Elecrow-RD/CrowPanel-ESP32-1.54-E-paper-HMI-Display-with-152-152/factory_soucecode/1.54_tow/pic/154/154/NEW_UI_1-54_BW_拨轮页面-01.bmp

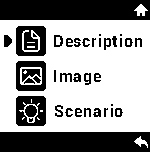
factory_soucecode/1.54_tow/pic/154/154/NEW_UI_1-54_BW_拨轮页面-01.bmp
