Elecrow-RD/CrowPanel-ESP32-1.54-E-paper-HMI-Display-with-152-152/factory_soucecode/1.54_tow/pic/NEW_UI_1-54_BW_/NEW_UI_1-54_BW_img-04.bmp

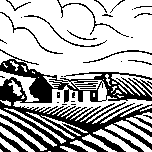
factory_soucecode/1.54_tow/pic/NEW_UI_1-54_BW_/NEW_UI_1-54_BW_img-04.bmp
