Elecrow-RD/CrowPanel-ESP32-1.54-E-paper-HMI-Display-with-152-152/factory_soucecode/1.54_tow/pic/ui_1-54_BW/UI_1-54_BW_img-06.bmp

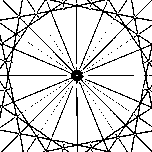
factory_soucecode/1.54_tow/pic/ui_1-54_BW/UI_1-54_BW_img-06.bmp
