Elecrow-RD/CrowPanel-ESP32-1.54-E-paper-HMI-Display-with-152-152/factory_soucecode/1.54_tow/main/pic_image.h

const unsigned char gImage_image[2888] = { /* 0X00,0X01,0X98,0X00,0X98,0X00, */
0X00,0X00,0X00,0X1C,0X00,0X00,0X01,0XC0,0X00,0X00,0X00,0X06,0X00,0X00,0X00,0X00,
0X00,0X00,0XC0,0X00,0X00,0X00,0X07,0X00,0X00,0X07,0X00,0X00,0X00,0X00,0X04,0X00,
0X00,0X00,0X00,0X00,0X03,0X80,0X00,0X00,0X00,0X01,0X80,0X00,0X0C,0X00,0X00,0X00,
0X00,0X0C,0X00,0X00,0X00,0X70,0X00,0X06,0X00,0X00,0X00,0X00,0X00,0XC0,0X00,0X18,
0X00,0X01,0XFF,0XE0,0X08,0X00,0X00,0X00,0X0E,0X00,0X0C,0X00,0X00,0X00,0X00,0X00,
0X60,0X00,0X30,0X00,0X0F,0X80,0X7C,0X18,0X00,0X00,0X00,0X03,0X80,0X08,0X00,0X00,
0X00,0X00,0X00,0X10,0X00,0X60,0X00,0X3C,0X00,0X07,0X10,0X00,0X00,0X00,0X00,0XE0,
0X18,0X00,0XFF,0XF0,0X00,0X00,0X08,0X00,0XC0,0X00,0X70,0X00,0X01,0XB0,0X00,0X00,
0X00,0X00,0X38,0X30,0X00,0X00,0X1F,0X00,0X00,0X04,0X00,0X80,0X00,0XC0,0X00,0X00,
0XE0,0X00,0X00,0X00,0X00,0X0E,0X20,0X00,0X00,0X00,0XC0,0X00,0X02,0X01,0X00,0X01,
0X80,0X00,0X00,0X20,0X00,0X00,0X00,0X00,0X03,0X60,0X00,0X00,0X00,0X10,0X00,0X01,
0X03,0X00,0X03,0X00,0X00,0X00,0X20,0X00,0X00,0X00,0X00,0X01,0XC0,0X00,0X00,0X00,
0X00,0X00,0X01,0X02,0X00,0X06,0X00,0X00,0X00,0X60,0X00,0X00,0X00,0X00,0X00,0XC0,
0X00,0X00,0X00,0X00,0X00,0X00,0X86,0X00,0X0C,0X00,0X00,0X00,0X60,0X00,0X00,0X00,
0X00,0X00,0X00,0X00,0X00,0X00,0X00,0X00,0X00,0X44,0X00,0X18,0X00,0X00,0X00,0X60,
0X00,0X00,0X00,0X00,0X00,0X00,0X07,0X3F,0XE0,0X00,0X00,0X00,0X00,0X00,0X10,0X00,
0X00,0X00,0X40,0X00,0X00,0X00,0X00,0X00,0X00,0X1C,0XF0,0X7C,0X00,0X00,0X00,0X0F,
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
0X00,0X00,0X00,0X03,0XFF,0XFF,0XF0,0X00,0X01,0XE0,0X00,0X0C,0X00,0X00,0X00,0X00,
0X00,0XE0,0X00,0X00,0X00,0X00,0X00,0X7F,0XFE,0X00,0X00,0X00,0XF0,0X00,0X06,0X00,
0X00,0X00,0X00,0X00,0X78,0X00,0X00,0X00,0X00,0X00,0X07,0X80,0X00,0X00,0X00,0X78,
0X00,0X01,0X00,0X00,0X00,0X00,0X00,0X1E,};
