Elecrow-RD/CrowPanel-ESP32-1.54-E-paper-HMI-Display-with-152-152/factory_soucecode/1.54_tow/main/pic_scenario.h

const unsigned char gImage_scenario_home[2888] = { /* 0X00,0X01,0X98,0X00,0X98,0X00, */
0XFF,0XFF,0XFF,0XFF,0XFF,0XFF,0XFF,0XFF,0XFF,0XFF,0XFF,0XFF,0XFF,0XFF,0XFF,0XFF,
0XFF,0XFF,0XFF,0XFF,0XFF,0XFF,0XFF,0XFF,0XFF,0XFF,0XFF,0XFF,0XFF,0XFF,0XFF,0XFF,
0XFF,0XFF,0XFF,0XFF,0XFF,0XFF,0XFF,0XFF,0XFF,0XFF,0XFF,0XFF,0XFF,0XFF,0XFF,0XFF,
0XFF,0XFF,0XFF,0XFF,0XFF,0XFF,0XFF,0XE7,0XFF,0XFF,0XFF,0XFF,0XFF,0XFF,0XFF,0XFF,
0XFF,0XFF,0XFF,0XFF,0XFF,0XFF,0XFF,0XFF,0XFF,0XFF,0XE7,0XFF,0XFF,0XCF,0XFF,0XFF,
0XF3,0XFF,0XFF,0XFF,0XFF,0XFF,0XFF,0XFF,0XFF,0XFF,0XFF,0XFF,0XFC,0XFF,0X3F,0XFF,
0X87,0XFF,0XFF,0XF3,0XFF,0XFF,0X9F,0XFF,0XFF,0X0F,0XFF,0XFF,0XFF,0XFF,0XF9,0XFE,
0X81,0X7F,0XFF,0X03,0XFF,0XFF,0XF3,0XFF,0XFF,0X9F,0XFF,0XFE,0X47,0XFF,0XFF,0XFF,
0XFF,0XF9,0XFF,0X3C,0XFF,0XFE,0X01,0XFF,0XFF,0XF3,0XC3,0XD7,0X0E,0X2E,0X1C,0XE7,
0XF8,0XB8,0X8B,0XE3,0XF9,0XFF,0X7E,0XFF,0XFC,0X00,0XFF,0XFF,0XF3,0XC9,0XE7,0X9C,
0X4E,0X4F,0XF7,0XF1,0X39,0X13,0XC9,0XF9,0XFE,0X7E,0X7F,0XF8,0X00,0X7F,0XFF,0XF3,
0X9D,0XE7,0X9C,0XCC,0XEF,0XF7,0XF3,0X33,0X33,0XCF,0XF9,0XF2,0X7E,0X4F,0XF0,0X00,
0X3F,0XFF,0XF3,0X9C,0XE7,0X9C,0XCC,0XE7,0XF7,0XF3,0X33,0X33,0XC1,0XF9,0XFE,0X7E,
0X7F,0XFE,0X01,0XFF,0XFF,0XF3,0X9D,0XE7,0X9C,0XCC,0XEC,0XE7,0XF3,0X33,0X33,0XCC,
0XF9,0XFF,0X3E,0XFF,0XFE,0X01,0XFF,0XFF,0XF3,0XC9,0XE7,0X9C,0XCE,0X4E,0X47,0XF1,
0X33,0X33,0XC8,0XF9,0XFF,0XBD,0XFF,0XFE,0X31,0XFF,0XFF,0XF3,0XC3,0XE7,0X3C,0XCE,
0X1F,0X0F,0XF8,0X33,0X33,0XD1,0X81,0XFE,0X9F,0X7F,0XFE,0X31,0XFF,0XFF,0XFF,0XFF,
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
0X00,0X80,0X20,0X99,0X87,0XF9,0X00,0X00,0X80,0X20,0X99,0X07,0XF9,0X00,0X00,0XC0,
0X20,0X8E,0X03,0XF3,0X00,0X00,0X40,0X00,0X00,0X01,0XE2,0X00,0X00,0X20,0X00,0X00,
0X00,0X04,0X00,0X00,0X18,0X00,0X00,0X00,0X18,0X00,0X00,0X0F,0XFF,0XFF,0XFF,0XF0,
0X00,0X00,};
