Elecrow-RD/CrowPanel-ESP32-1.54-E-paper-HMI-Display-with-152-152/example/arduino/Example/1.54_Global_refresh/Pic.h

const unsigned char gImage_1[2888] = { /* 0X00,0X01,0X98,0X00,0X98,0X00, */
0XFF,0XFF,0XFF,0XFF,0XFF,0XFF,0XFF,0XFF,0XFF,0XFF,0XFF,0XFF,0XFF,0XFF,0XFF,0XFF,
0XFF,0XFF,0XFF,0XFF,0XFF,0XFF,0XFF,0XFF,0XFF,0XFF,0XFF,0XFF,0XFF,0XFF,0XFF,0XFF,
0XFF,0XFF,0XFF,0XFF,0XFF,0XFF,0XFF,0XFF,0XFF,0XFF,0XFF,0XFF,0XFF,0XFF,0XFF,0XFF,
0XFF,0XFF,0XFF,0XFF,0XFF,0XFF,0XFF,0XFF,0XFF,0XFF,0XFF,0XFF,0XFF,0XFF,0XFF,0XFF,
0XFF,0XFF,0XFF,0XFF,0XFF,0XFF,0XFF,0XFF,0XFF,0XFF,0XFF,0XFF,0XFF,0XFF,0XFF,0XFF,
0XFF,0XFF,0XFF,0XFF,0XFF,0XFF,0XFF,0XFF,0XFF,0XFF,0XFF,0XFF,0XFF,0XFF,0XFF,0XFF,
0XFF,0XFF,0XFF,0XFF,0XFF,0XFF,0XFF,0XFF,0XFF,0XFF,0XFF,0XFF,0XFF,0XFF,0XFF,0XFF,
0XFF,0XFF,0XFF,0XFF,0XFF,0XFF,0XFF,0XFF,0XFF,0XF0,0X1F,0X9F,0XFF,0XFF,0XFE,0X07,
0XFF,0XFF,0XFF,0XC3,0XFF,0XFF,0XFF,0XFF,0XFF,0XFF,0XFF,0XFF,0XF0,0X1F,0X9F,0XFF,
0XFF,0XFC,0X07,0XFF,0XFF,0XFF,0X01,0XFF,0XFF,0XFF,0XFF,0XFF,0XFF,0XFF,0XFF,0XFF,
0X9F,0X9F,0XFF,0XFF,0XF9,0XE7,0XFF,0XFF,0XFF,0X38,0XFF,0XFF,0XFF,0X86,0X0E,0X07,
0X0E,0X07,0XFF,0X9F,0X98,0X38,0X1C,0X39,0XE4,0XC6,0X60,0XC3,0X3C,0XFF,0XFF,0XFF,
0X86,0X04,0X06,0X04,0X07,0XFF,0X9F,0X98,0X10,0X18,0X19,0XE4,0XC4,0X40,0X43,0XFC,
0XFF,0XFF,0XFF,0XE4,0X64,0XE6,0X64,0XE7,0XF0,0X1F,0X91,0X91,0X99,0X98,0X04,0X44,
0XCE,0X73,0XFC,0X7F,0XFF,0XFF,0XE4,0X00,0XE6,0X0C,0XE4,0X1F,0X9F,0X90,0X01,0X98,
0X3C,0X06,0X04,0XCE,0X33,0XFC,0XFF,0XFF,0XFF,0XE4,0X00,0XE6,0X44,0XE7,0XFF,0X9F,
0X90,0X01,0X99,0X1F,0XE6,0X10,0XCE,0X33,0X3C,0XFF,0XFF,0XFF,0XE7,0XE0,0XE6,0X60,
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
0XFF,0XFF,0XFF,0XFF,0XFF,0XFF,0XFF,0XFF,0XFF,0XFF,0XFF,0XFF,0XFF,0XFF,0XFF,0XFF,
0XFF,0XFF,0XFF,0XFF,0XFF,0XFF,0XFF,0XFF,0XFF,0XFF,0XFF,0XFF,0XFF,0XFF,0XFF,0XFF,
0XFF,0XFF,0XFF,0XFF,0XFF,0XFF,0XFF,0XFF,0XFF,0XFF,0XFF,0XFF,0XFF,0XFF,0XFF,0XFF,
0XFF,0XFF,0XFF,0XFF,0XFF,0XFF,0XFF,0XFF,};
