Elecrow-RD/CrowPanel-ESP32-1.54-E-paper-HMI-Display-with-152-152/example/arduino/Example/1.54_PWR/Pic.h

const unsigned char gImage_3[480] = { /* 0X00,0X01,0X50,0X00,0X30,0X00, */
0X1F,0XFF,0XFF,0XFF,0XFF,0XFF,0XFF,0XFF,0XFF,0XF8,0X0F,0XFF,0XFF,0XFF,0XFF,0XFF,
0XFF,0XFF,0XFF,0XF8,0X07,0XFF,0XFF,0XFF,0XFF,0XFF,0XFF,0XFF,0XFF,0XF8,0X03,0XFF,
0XFF,0XFF,0XFF,0XFF,0XFF,0XFF,0XFF,0XF8,0X01,0XFF,0XFE,0X4F,0XBF,0X7F,0XFF,0XFF,
0XFB,0XF8,0X00,0X7F,0XFE,0X06,0X0F,0X7F,0X3F,0XFF,0XE0,0XF8,0X00,0X3F,0X77,0X02,
0X6F,0X33,0XF7,0XDE,0XE6,0XF8,0X00,0X1C,0X03,0X02,0XE7,0X21,0X21,0X0C,0X1C,0XF8,
0X00,0X1F,0X01,0XB2,0X67,0X21,0X2D,0X04,0X90,0XF8,0X00,0X3F,0X01,0X92,0X67,0X20,
0XBC,0X04,0X83,0X78,0X00,0X7F,0X2D,0X92,0X67,0XA4,0X84,0XB4,0X96,0X78,0X00,0XFF,
0XA1,0X93,0X0F,0X80,0X91,0X86,0X10,0X78,0X01,0XFF,0XFF,0XFF,0XFF,0XFF,0XFF,0XFF,
0XCF,0XF8,0X03,0XFF,0XFF,0XFF,0XFF,0XFF,0XFF,0XFF,0XCF,0XF8,0X07,0XFF,0XFF,0XFF,
0XFF,0XFF,0XFF,0XFF,0XFF,0XF8,0X0F,0XFF,0XFF,0XFF,0XFF,0XFF,0XFF,0XFF,0XFF,0XF8,
0X1F,0XFF,0XFF,0XFF,0XFF,0XFF,0XFF,0XFF,0XFF,0XF8,0X00,0X00,0X00,0X00,0X00,0X00,
0X00,0X00,0X00,0X00,0X00,0X00,0X00,0X00,0X00,0X00,0X00,0X00,0X00,0X00,0X00,0X00,
0X00,0X00,0X00,0X00,0X00,0X00,0X00,0X00,0X00,0X00,0X00,0X00,0X00,0X00,0X00,0X00,
0X00,0X00,0X00,0X00,0X00,0X00,0X00,0X00,0X00,0X00,0X00,0X00,0X00,0X00,0X00,0X00,
0X00,0X00,0X00,0X00,0X00,0X00,0X00,0X00,0X00,0X00,0X00,0X00,0X00,0X00,0X00,0X00,
0X00,0X00,0X00,0X00,0X00,0X00,0X00,0X18,0X00,0X00,0X00,0X00,0X00,0X00,0X00,0X00,
0X00,0X18,0X00,0X00,0X00,0X78,0X00,0XE0,0X00,0X18,0X00,0X3C,0X00,0X00,0X01,0XFE,
0X03,0XF8,0X00,0X1F,0X00,0XFF,0X00,0X00,0X03,0XFE,0X07,0XFC,0X00,0X1F,0X80,0XFF,
0X80,0X00,0X03,0X8F,0X0F,0X1C,0X00,0X07,0XC1,0XE3,0X80,0X00,0X07,0X87,0X0E,0X0E,
0X00,0X01,0XE1,0XC3,0XC0,0X00,0X07,0X07,0X8E,0X0E,0X00,0X00,0XE1,0XC1,0XC0,0X00,
0X07,0X03,0X9E,0X0E,0X00,0X00,0XE0,0X03,0X80,0X00,0X07,0X03,0X9C,0X0E,0X00,0X3F,
0XF0,0X07,0X80,0X00,0X07,0X03,0X9E,0X1E,0X00,0X7F,0XF0,0X3F,0X80,0X00,0X07,0X03,
0X9F,0X1C,0X00,0X78,0XF0,0X7E,0X00,0X00,0X07,0X03,0X8F,0XFC,0X00,0XF0,0X70,0XF8,
0X00,0X00,0X07,0X03,0X8F,0XF8,0X00,0XE0,0X71,0XE0,0X00,0X00,0X07,0X03,0X8E,0X00,
0X00,0XE0,0X71,0XC0,0X00,0X00,0X07,0X07,0X8E,0X00,0X00,0XE0,0X71,0XC1,0XC0,0X00,
0X07,0X87,0X07,0X00,0X00,0XF0,0XE1,0XC1,0XC0,0X00,0X03,0X8F,0X07,0XC0,0X18,0X79,
0XE1,0XE3,0XC0,0X00,0X03,0XFE,0X03,0XF0,0X38,0X7F,0XC1,0XFF,0X80,0X00,0X01,0XFC,
0X00,0XF0,0X38,0X3F,0X80,0XFF,0X00,0X00,0X00,0X30,0X00,0X00,0X00,0X06,0X00,0X1C,
0X00,0X00,0X00,0X00,0X00,0X00,0X00,0X00,0X00,0X18,0X00,0X00,0X00,0X00,0X00,0X00,
0X00,0X00,0X00,0X18,0X00,0X00,0X00,0X00,0X00,0X00,0X00,0X00,0X00,0X00,0X00,0X00,
};
